guillaumef/cg-scale-wifi-oled/pix/big/photo-board-stormbird-ballast.jpg

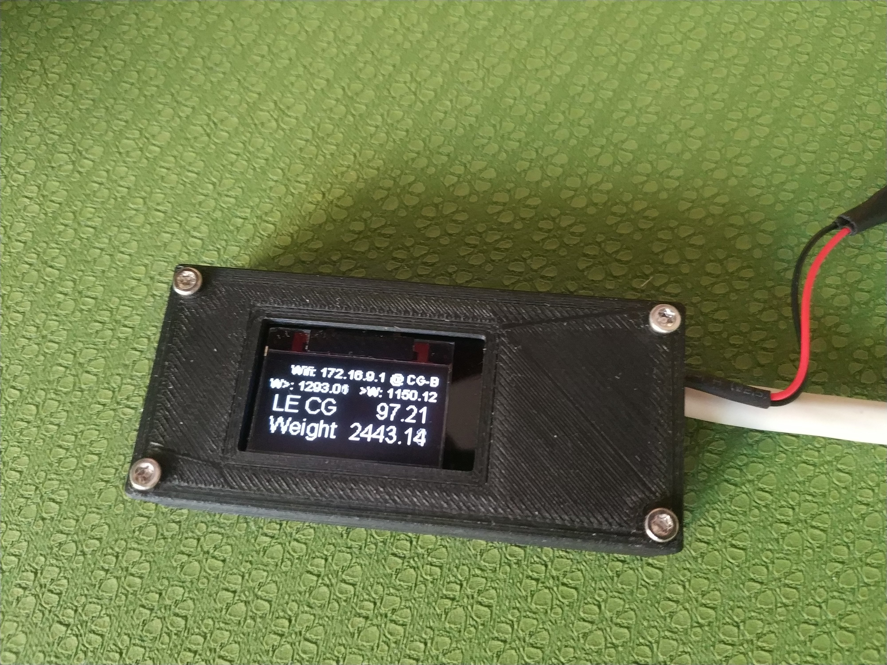
pix/big/photo-board-stormbird-ballast.jpg
