guillaumef/cg-scale-wifi-oled/pix/big/photo-board.jpg

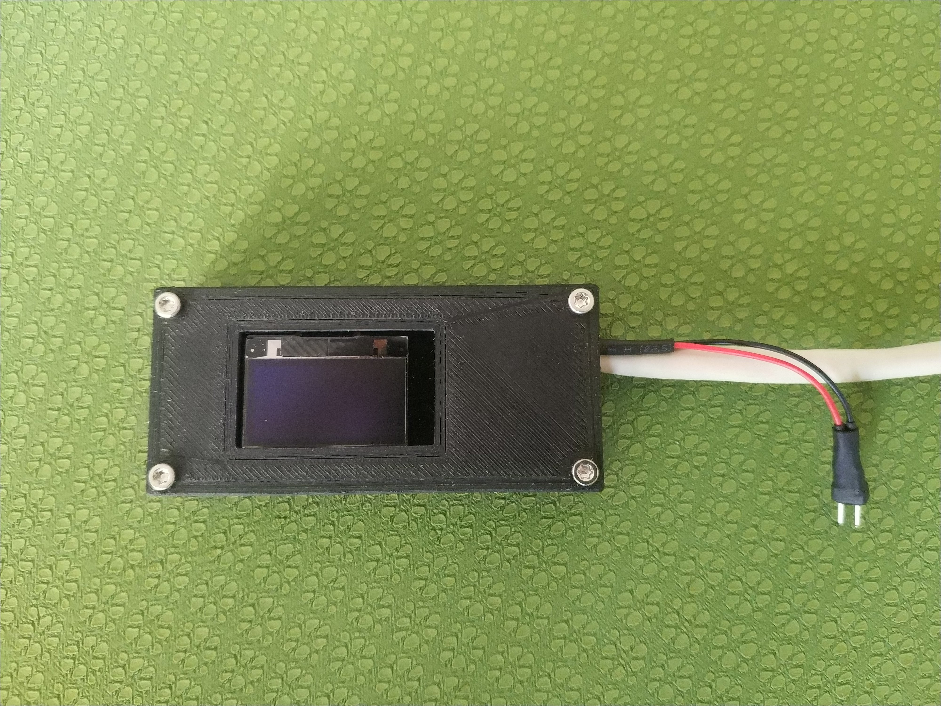
pix/big/photo-board.jpg
