guillaumef/cg-scale-wifi-oled/pix/big/photo-bottom.jpg

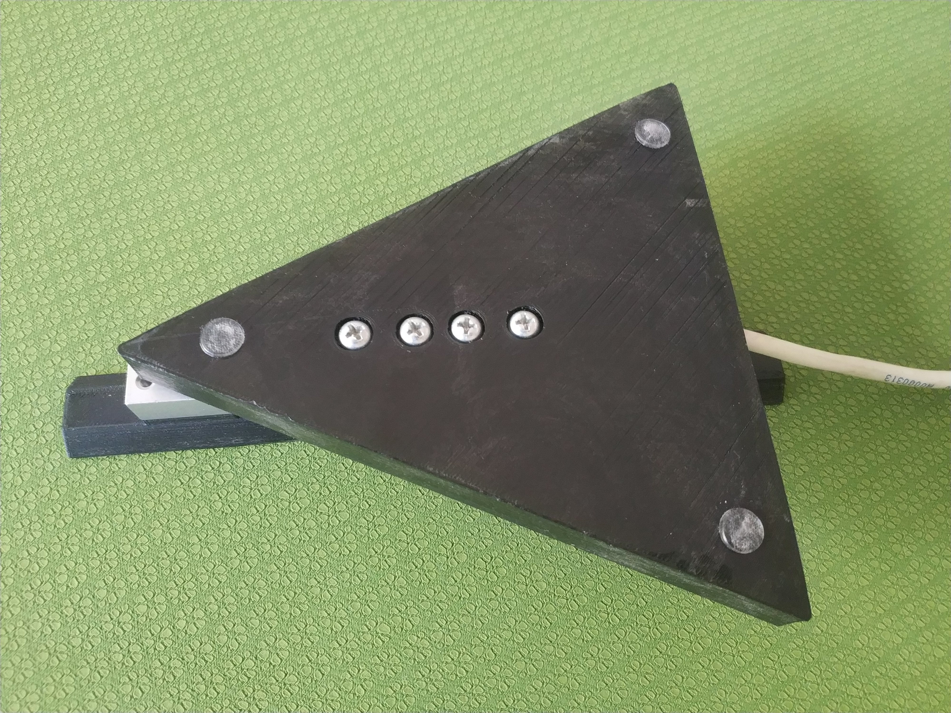
pix/big/photo-bottom.jpg
