guillaumef/cg-scale-wifi-oled/pix/big/photo-loading1.jpg

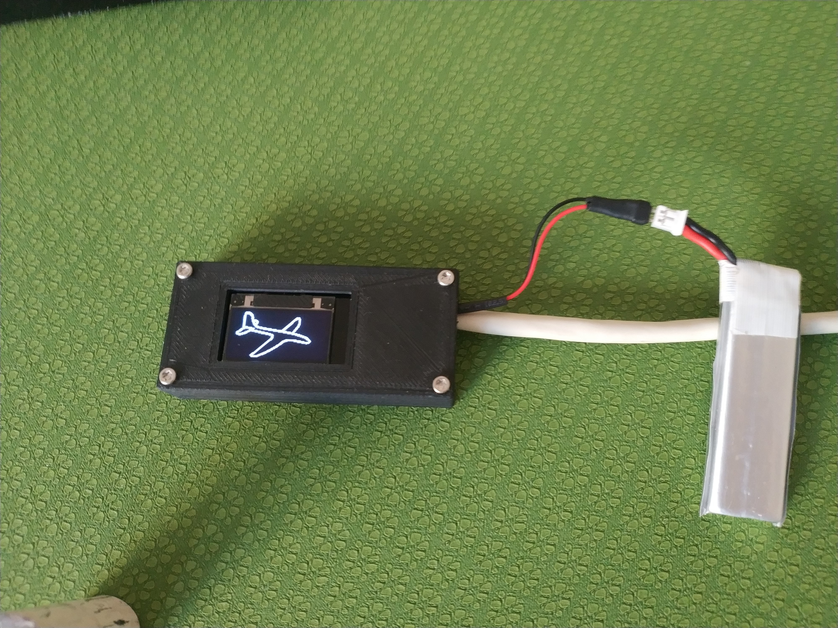
pix/big/photo-loading1.jpg
