guillaumef/cg-scale-wifi-oled/pix/big/photo-loading2.jpg

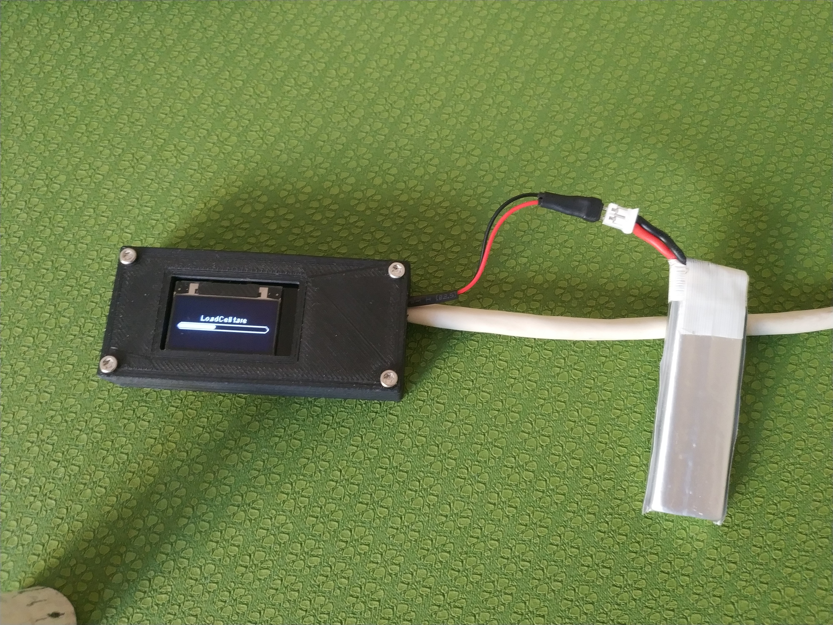
pix/big/photo-loading2.jpg
