guillaumef/cg-scale-wifi-oled/pix/big/photo-stormbird2.jpg

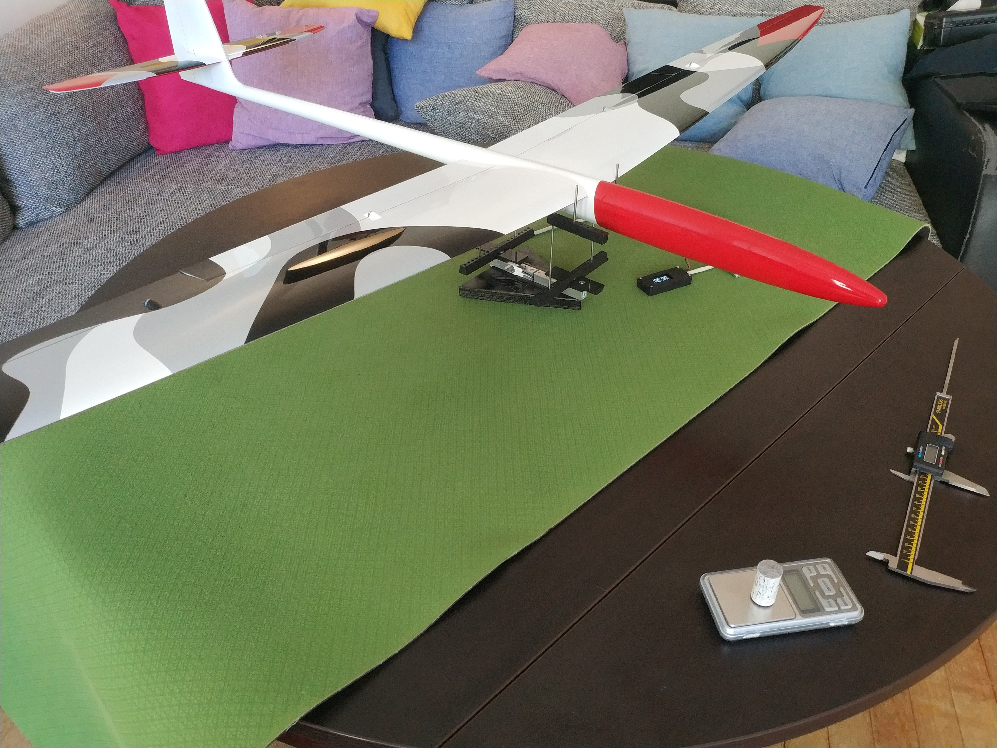
pix/big/photo-stormbird2.jpg
