guillaumef/cg-scale-wifi-oled/pix/big/photo-stormbird4.jpg

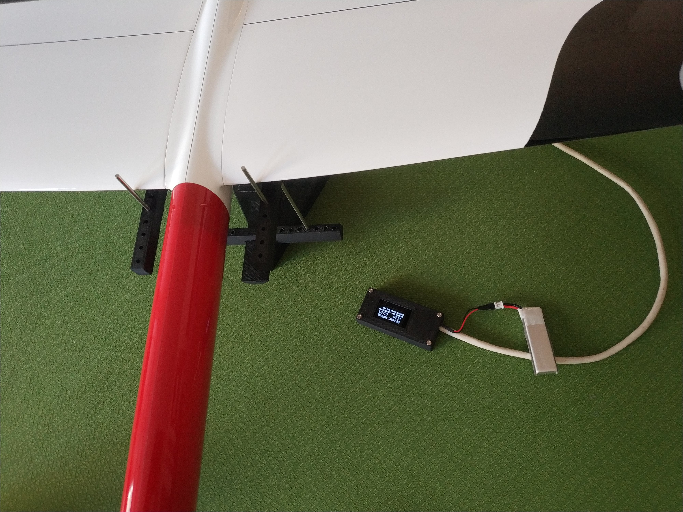
pix/big/photo-stormbird4.jpg
