guillaumef/cg-scale-wifi-oled/pix/big/photo-stormbird-balast.jpg

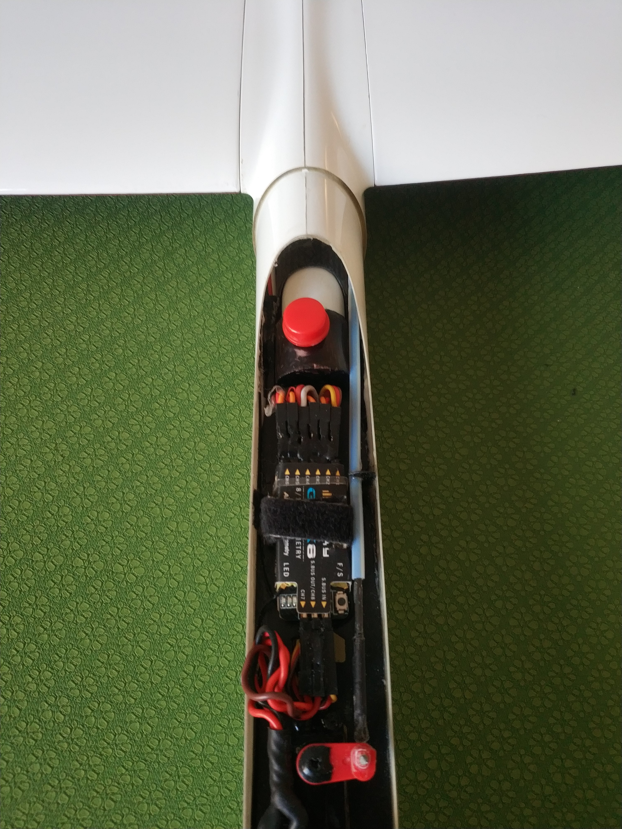
pix/big/photo-stormbird-balast.jpg
