guillaumef/cg-scale-wifi-oled/pix/big/screenshot-menu.jpg

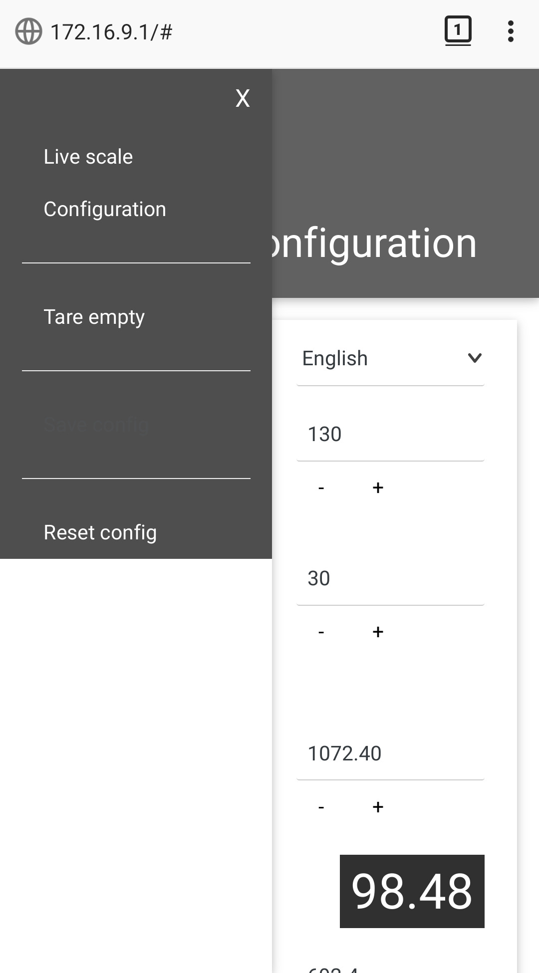
pix/big/screenshot-menu.jpg
