guillaumef/cg-scale-wifi-oled/pix/big/screenshot-tare.jpg

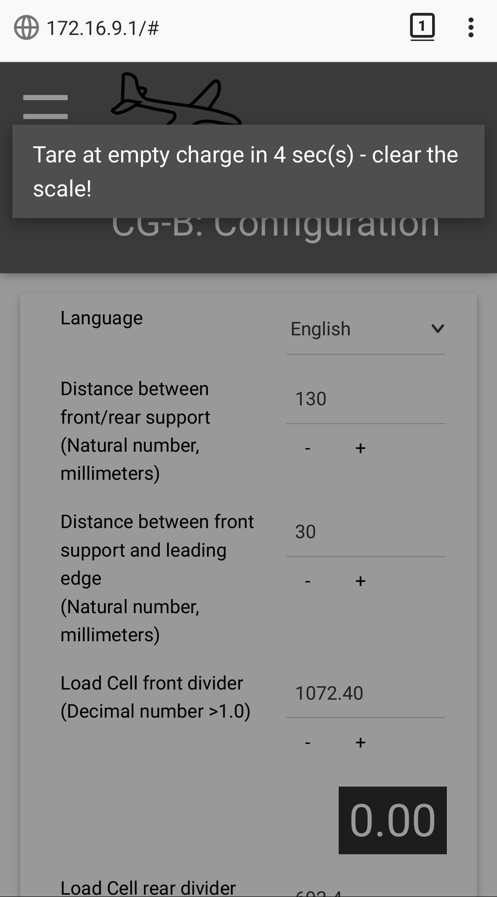
pix/big/screenshot-tare.jpg
