guillaumef/cg-scale-wifi-oled/pix/bom-hx711.jpg

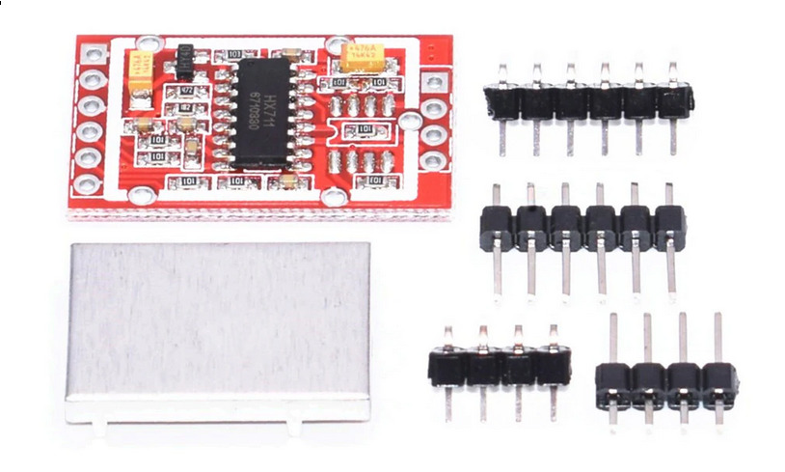
pix/bom-hx711.jpg
