guillaumef/cg-scale-wifi-oled/pix/big/photo-assembly1.jpg

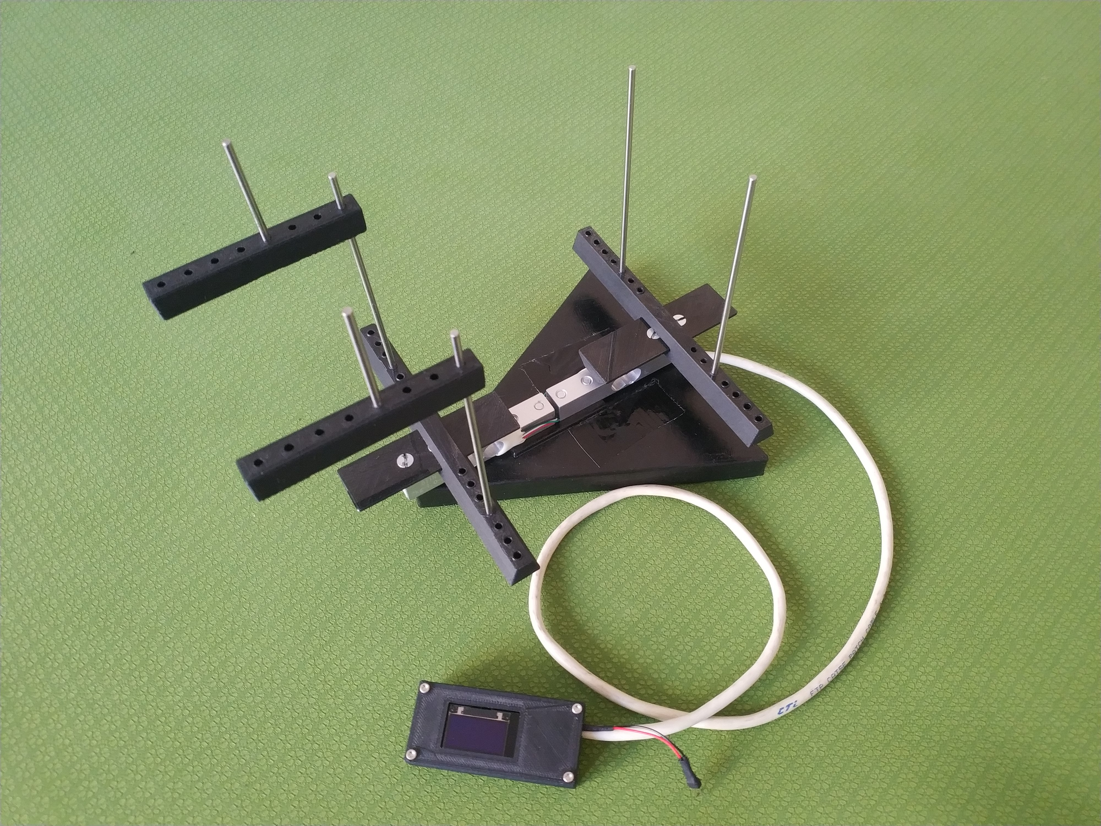
pix/big/photo-assembly1.jpg
