guillaumef/cg-scale-wifi-oled/pix/big/photo-assembly2.jpg

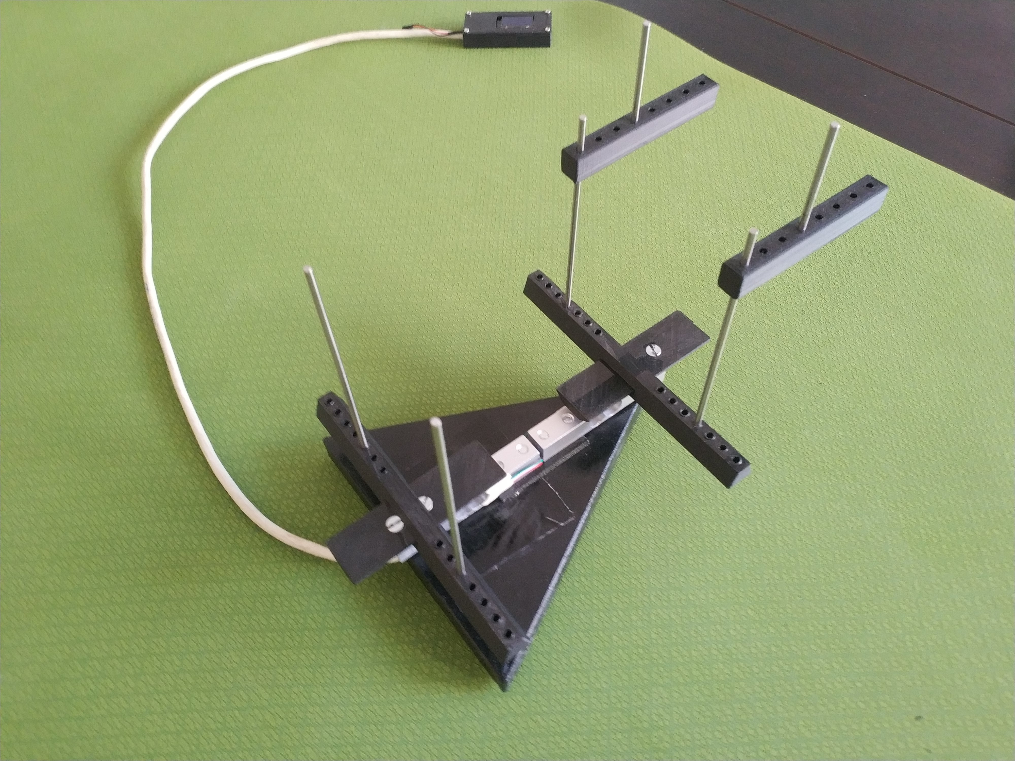
pix/big/photo-assembly2.jpg
